dpeckett/cat-tracker/firmware/BSP/E77-900M22S/ADC/adc.c

/*
 * Copyright (c) 2021 STMicroelectronics.
 * All rights reserved.
 *
 * This software is licensed under terms that can be found in the LICENSE file
 * in the root directory of this software component.
 * If no LICENSE file comes with this software, it is provided AS-IS.
 *
 */

#include "adc.h"

ADC_HandleTypeDef hadc;

/* ADC init function */
void MX_ADC_Init(void) {
  /** Configure the global features of the ADC (Clock, Resolution, Data
   * Alignment and number of conversion)
   */
  hadc.Instance = ADC;
  hadc.Init.ClockPrescaler = ADC_CLOCK_SYNC_PCLK_DIV4;
  hadc.Init.Resolution = ADC_RESOLUTION_12B;
  hadc.Init.DataAlign = ADC_DATAALIGN_RIGHT;
  hadc.Init.ScanConvMode = ADC_SCAN_DISABLE;
  hadc.Init.EOCSelection = ADC_EOC_SINGLE_CONV;
  hadc.Init.LowPowerAutoWait = DISABLE;
  hadc.Init.LowPowerAutoPowerOff = DISABLE;
  hadc.Init.ContinuousConvMode = DISABLE;
  hadc.Init.NbrOfConversion = 1;
  hadc.Init.DiscontinuousConvMode = DISABLE;
  hadc.Init.ExternalTrigConv = ADC_SOFTWARE_START;
  hadc.Init.ExternalTrigConvEdge = ADC_EXTERNALTRIGCONVEDGE_NONE;
  hadc.Init.DMAContinuousRequests = DISABLE;
  hadc.Init.Overrun = ADC_OVR_DATA_OVERWRITTEN;
  hadc.Init.SamplingTimeCommon1 = ADC_SAMPLETIME_160CYCLES_5;
  hadc.Init.SamplingTimeCommon2 = ADC_SAMPLETIME_160CYCLES_5;
  hadc.Init.OversamplingMode = DISABLE;
  hadc.Init.TriggerFrequencyMode = ADC_TRIGGER_FREQ_HIGH;
  if (HAL_ADC_Init(&hadc) != HAL_OK) {
    // Nop for now.
  }
}

void HAL_ADC_MspInit(ADC_HandleTypeDef *adcHandle) {
  if (adcHandle->Instance == ADC) {
    __HAL_RCC_ADC_CLK_ENABLE();
  }
}

void HAL_ADC_MspDeInit(ADC_HandleTypeDef *adcHandle) {

  if (adcHandle->Instance == ADC) {
    /* Peripheral clock disable */
    __HAL_RCC_ADC_CLK_DISABLE();
  }
}
